Ivanchenko59/SMD_counter/images/case2.jpg

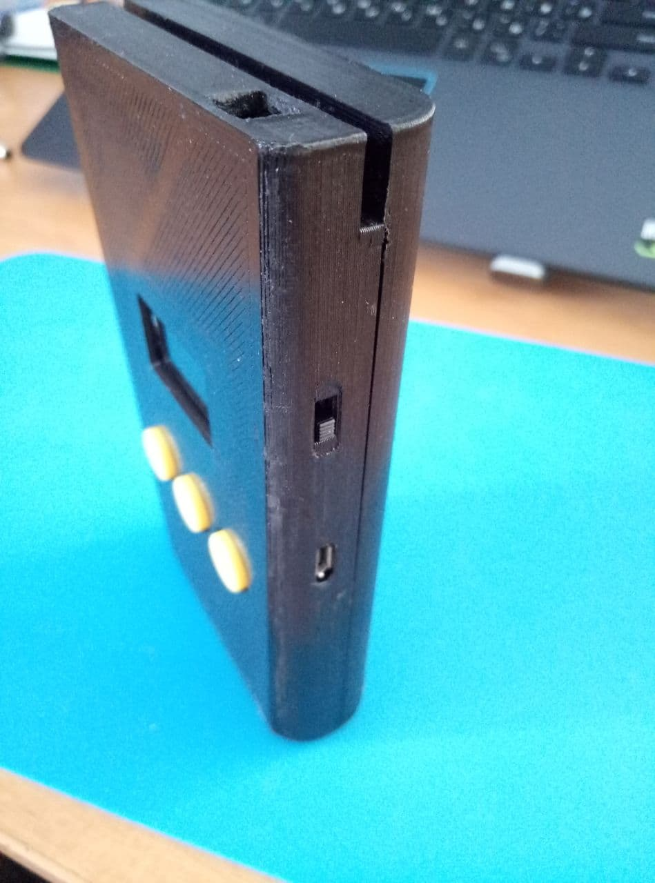
images/case2.jpg
