Ivanchenko59/SMD_counter/images/database.jpg

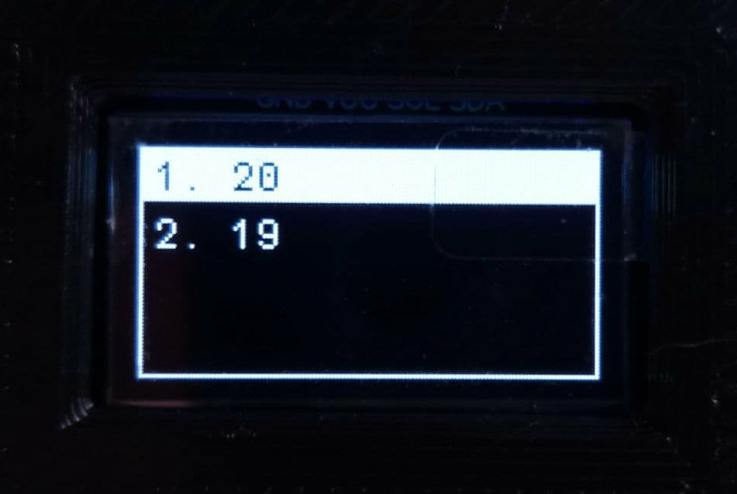
images/database.jpg
