Ivanchenko59/SMD_counter/images/photoresist.jpg

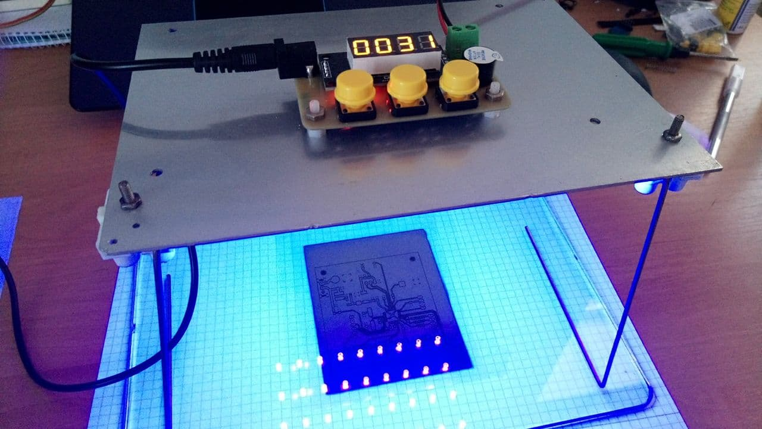
images/photoresist.jpg
